sinara-hw/Fastino/SIM_CALC/Output stage/Design.asc

C1: cap; 10p
C2: cap; 47p
C3: cap; 360p
C4: cap; 100p
R1: res; {Rdac}
R2: res; 1.47k
R3: res; {Rinv}
R4: res; {Rinv/2}
R5: res; {Rinv}
R6: res; 0
R7: res; 1.69k
U1: opamp2; OPA197
U2: opamp2; OPA197
V1: voltage; 13
V2: voltage; -13
V3: voltage; PULSE(0 {Vref} 10u 10n 10n 10u); AC 1
V4: voltage; {Vref}
Named nets: 0, V+, V-, Vref, OUT
.include OPA197.lib
.param Rdac 6.2k
.param Rinv 10k
.param Vref 5.5
;.tran 30u
;.ac dec 100 1k 100Meg
.noise V(OUT) V3 dec 100 100 100Meg
