sinara-hw/Fastino/SIM_CALC/Output stage/Stabilizer output stage design.asc

C1: cap; 7.5p
C2: cap; 3.3p
C3: cap; 220p
C4: cap; 220p
C5: cap; 15p
R1: res; {Rdac}
R2: res; 560
R3: res; 10k
R4: res; {Rinv}
R5: res; {Rinv}
R6: res; 10k
R7: res; 1.58k
R8: res; 15k
U1: opamp2; AD8620
U2: opamp2; AD8620
V1: voltage; 13
V2: voltage; -13
V3: voltage; PULSE(0 {0.49 * Vref} 0 10n 10n 10u); AC 1
V4: voltage; {Vref}
Named nets: 0, V+, V-, Vref, OUT
.include AD8620.cir
.param Rdac 6.2k
.param Rinv 28k
.param Vref 4.096
;.tran 10u
.ac dec 100 1k 100Meg
;.noise V(OUT) V3 dec 100 100 100Meg
